Foquarion/Spartanpods/Inkscape Image Files/Raw Images/IMG_4669.JPEG

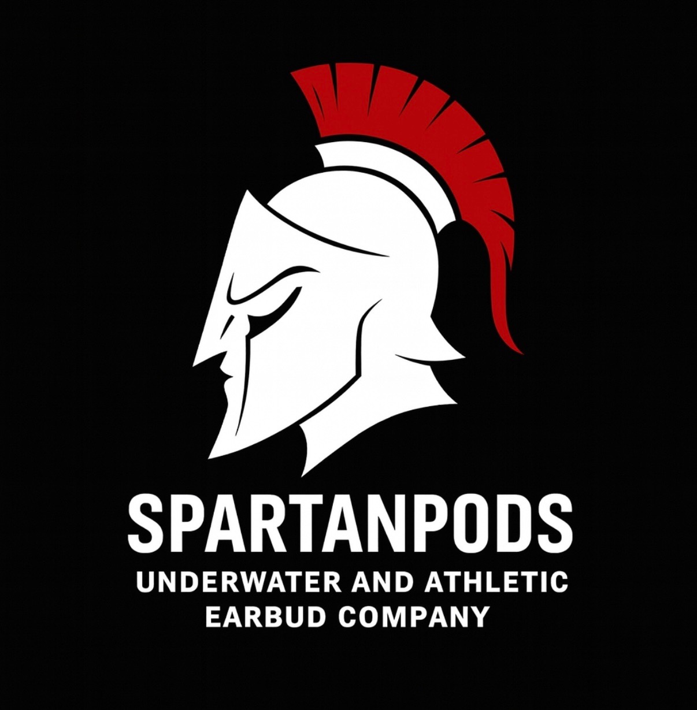
Inkscape Image Files/Raw Images/IMG_4669.JPEG
